kubafilinger/termostat-higrostat/eagle/lcd-i2c/lcd-i2c-pcb.png

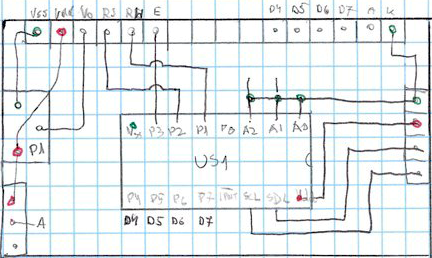
eagle/lcd-i2c/lcd-i2c-pcb.png
