kubafilinger/termostat-higrostat/eagle/relays-board/relays-board-schema.png

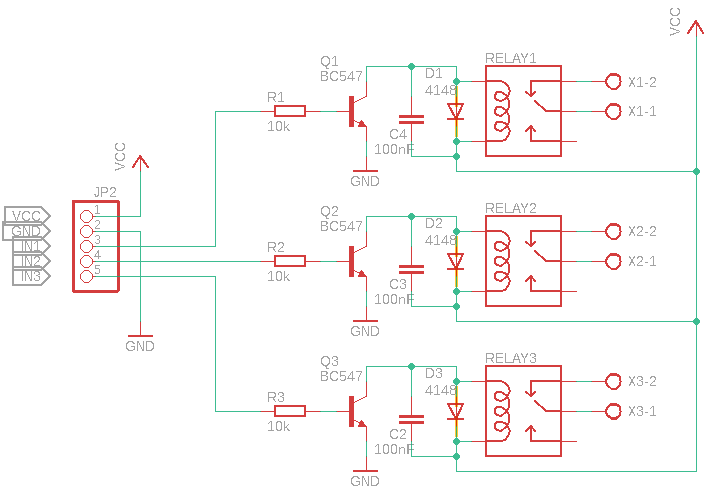
eagle/relays-board/relays-board-schema.png
