kubafilinger/termostat-higrostat/eagle/lcd-i2c/lcd-i2c.sch

## EAGLE design eagle/lcd-i2c/lcd-i2c.sch (2018-12-25)

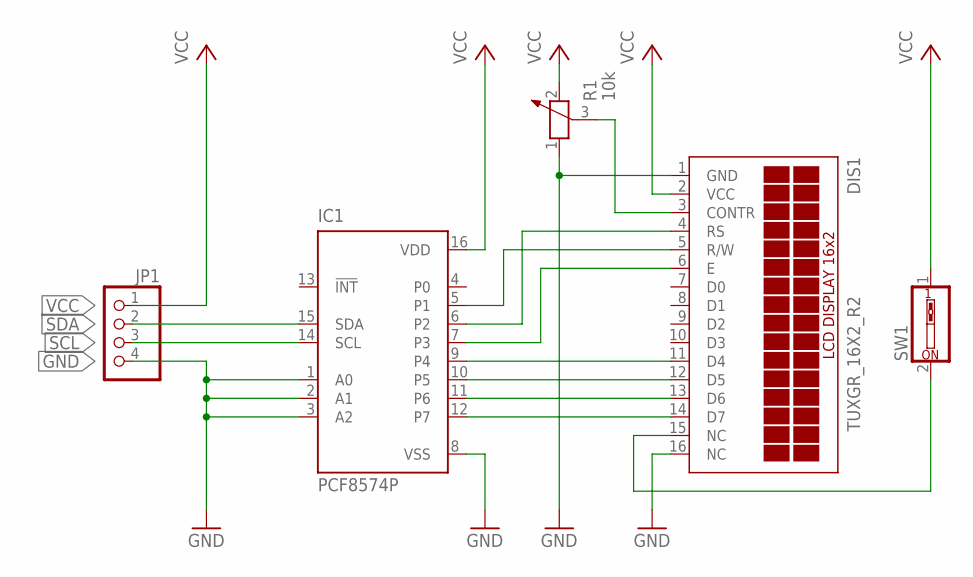
[picture p11: schematic lcd-i2c.sch]

Parts:
DIS1: TUXGR_16X2_R2
IC1: PCF8574P; DIL16
JP1: PINHD-1X4/90; 1X04/90
R1: 10k; PT-10S
SW1: SW_DIP-1; EDG-01

Connections:
GND: DIS1.1 (GND), DIS1.16 (NC), IC1.1 (A0), IC1.2 (A1), IC1.3 (A2), IC1.8 (VSS), JP1.4, R1.1
unnamed: DIS1.13 (D6), IC1.11 (P6)
unnamed: DIS1.15 (NC), SW1.2
unnamed: DIS1.14 (D7), IC1.12 (P7)
unnamed: DIS1.12 (D5), IC1.10 (P5)
unnamed: DIS1.11 (D4), IC1.9 (P4)
unnamed: DIS1.6 (E), IC1.7 (P3)
unnamed: DIS1.5 (R/W), IC1.5 (P1)
unnamed: DIS1.4 (RS), IC1.6 (P2)
unnamed: DIS1.3 (CONTR), R1.3
SCL: IC1.14 (SCL), JP1.3
SDA: IC1.15 (SDA), JP1.2
VCC: DIS1.2 (VCC), IC1.16 (VDD), JP1.1, R1.2, SW1.1
