kubafilinger/termostat-higrostat/eagle/mainboard/mainboard.sch

## EAGLE design eagle/mainboard/mainboard.sch (2019-04-16)

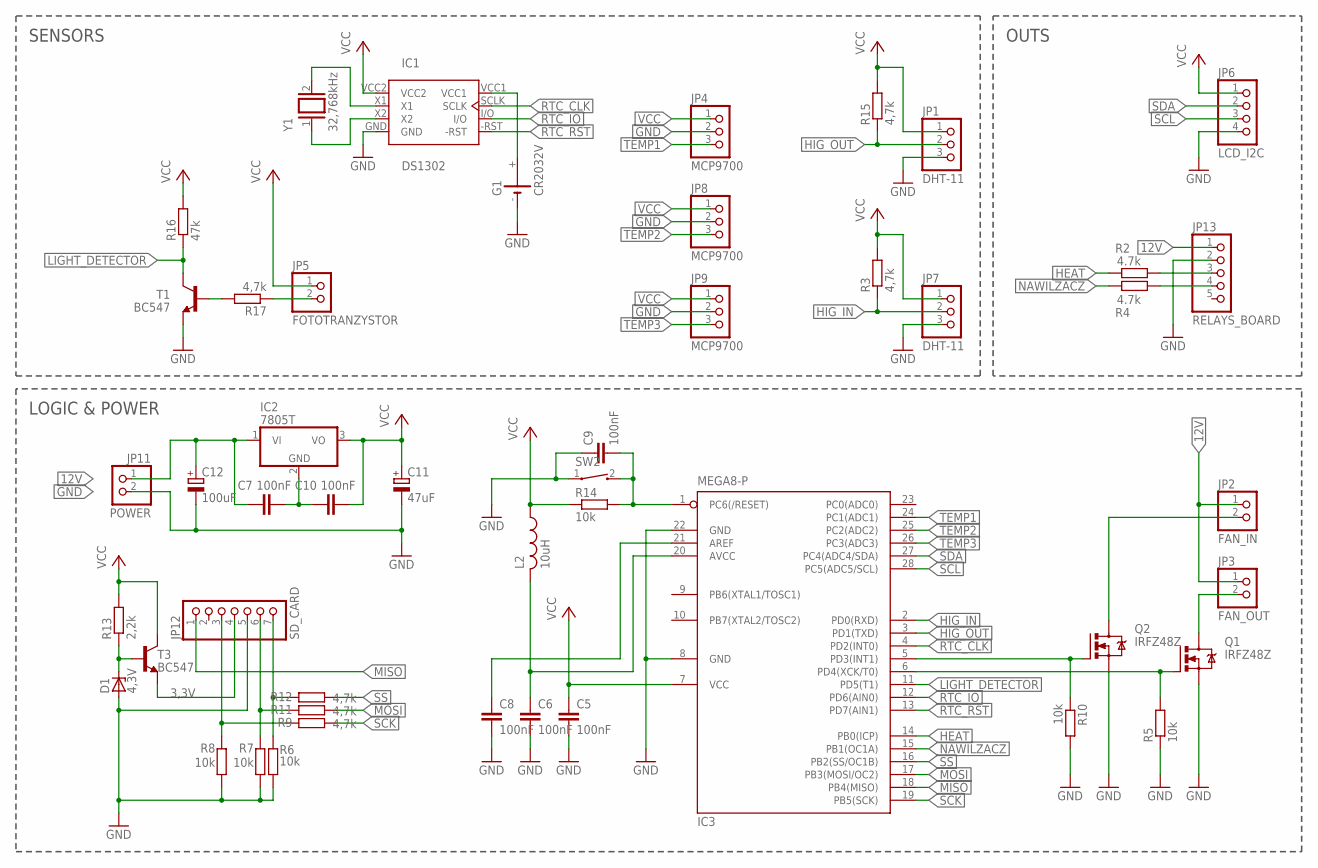
[picture p12: schematic mainboard.sch]

Parts:
C5, C6, C8, C9: 100nF; C050-030X075
C7, C10: 100nF; C050-024X044
C11: 47uF; E2,5-6
C12: 100uF; E2,5-6
D1: 4,3V; C1702-15
G1: CR2032V
IC1: DS1302; DIL08
IC2: 7805T; TO220H
IC3: MEGA8-P; DIL28-3
JP1, JP7: DHT-11; 1X03
JP2: FAN_IN; 1X02
JP3: FAN_OUT; 1X02
JP4, JP8, JP9: MCP9700; 1X03
JP5: FOTOTRANZYSTOR; 1X02
JP6: LCD_I2C; 1X04
JP11: POWER; 1X02
JP12: SD_CARD; 1X07
JP13: RELAYS_BOARD; 1X05
L2: 10uH; 0204/7
Q1, Q2: IRFZ48Z; TO220BH
R2, R4: 4.7k; 0207/10
R3, R9, R11, R12, R15, R17: 4,7k; 0207/10
R5, R6, R7, R8, R10: 10k; 0207/10
R13: 2,2k; 0207/10
R14: 10k; 0204/7
R16: 47k; 0207/10
SW2: CT10-XXXX-G4
T1, T3: BC547; TO92
Y1: 32,768kHz; QS

Connections:
3,3V: JP12.4, T3.1 (E)
12V: C7.1, C12.+, IC2.1 (VI), JP2.1, JP3.1, JP11.1, JP13.1
GND: C5.2, C6.2, C8.2, C9.1, C11.-, C12.-, D1.A, G1.-, IC1.GND, IC3.8 (GND), IC3.22 (GND), JP1.3, JP4.2, JP6.4, JP7.3, JP8.2, JP9.2, JP11.2, JP12.5, JP13.2, Q1.S, Q2.S, R5.1, R6.1, R7.1, R8.1, R10.2, SW2.1, T1.1 (E)
HEAT: IC3.14 (PB0(ICP)), R2.1
HIG_IN: IC3.2 (PD0(RXD)), JP7.2, R3.1
HIG_OUT: IC3.3 (PD1(TXD)), JP1.2, R15.1
LIGHT_DETECTOR: IC3.6 (PD4(XCK/T0)), IC3.11 (PD5(T1)), Q1.G, R5.2, R16.1, T1.3 (C)
MISO: IC3.18 (PB4(MISO)), JP12.1
MOSI: IC3.17 (PB3(MOSI/OC2)), R11.1
unnamed: JP13.3, R2.2
unnamed: IC1.X1, Y1.2
unnamed: JP13.4, R4.1
unnamed: C9.2, IC3.1 (PC6(/RESET)), R14.2, SW2.2
unnamed: JP5.2, R17.1
unnamed: C6.1, IC3.20 (AVCC), L2.2
unnamed: C8.1, IC3.21 (AREF)
unnamed: IC1.X2, Y1.1
unnamed: C7.2, C10.1, IC2.2 (GND)
unnamed: IC3.5 (PD3(INT1)), Q2.G, R10.1
unnamed: D1.C, R13.1, T3.2 (B)
unnamed: R17.2, T1.2 (B)
unnamed: JP2.2, Q2.D
unnamed: JP12.7, R6.2, R12.2
unnamed: JP3.2, Q1.D
unnamed: JP12.6, R7.2, R11.2
unnamed: JP12.3, R8.2, R9.2
NAWILZACZ: IC3.15 (PB1(OC1A)), R4.2
RTC_CLK: IC1.SCLK, IC3.4 (PD2(INT0))
RTC_IO: IC1.I/O, IC3.12 (PD6(AIN0))
RTC_RST: IC1.-RST, IC3.13 (PD7(AIN1))
SCK: IC3.19 (PB5(SCK)), R9.1
SCL: IC3.28 (PC5(ADC5/SCL)), JP6.3
SDA: IC3.27 (PC4(ADC4/SDA)), JP6.2
SS: IC3.16 (PB2(SS/OC1B)), R12.1
TEMP1: IC3.24 (PC1(ADC1)), JP4.3
TEMP2: IC3.25 (PC2(ADC2)), JP8.3
TEMP3: IC3.26 (PC3(ADC3)), JP9.3
VCC: C5.1, C10.2, C11.+, IC1.VCC2, IC2.3 (VO), IC3.7 (VCC), JP1.1, JP4.1, JP5.1, JP6.1, JP7.1, JP8.1, JP9.1, L2.1, R3.2, R13.2, R14.1, R15.2, R16.2, T3.3 (C)
VCC1: G1.+, IC1.VCC1

Notes on the sheet:
SENSORS
OUTS
LOGIC & POWER
