kubafilinger/termostat-higrostat/eagle/nawilzacz/nawilzacz.sch

## EAGLE design eagle/nawilzacz/nawilzacz.sch (2018-12-25)

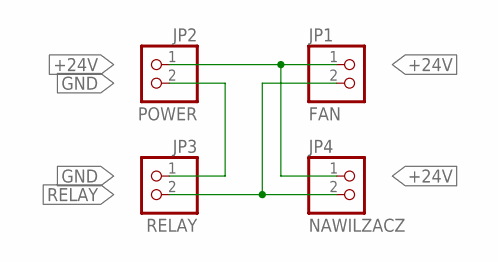
[picture p13: schematic nawilzacz.sch]

Parts:
JP1: FAN; 1X02
JP2: POWER; 1X02
JP3: RELAY; 1X02
JP4: NAWILZACZ; 1X02

Connections:
+24V: JP1.1, JP2.1, JP4.1
GND: JP2.2, JP3.1
RELAY: JP1.2, JP3.2, JP4.2
