kubafilinger/termostat-higrostat/eagle/relays-board/relays-board.sch

## EAGLE design eagle/relays-board/relays-board.sch (2018-12-25)

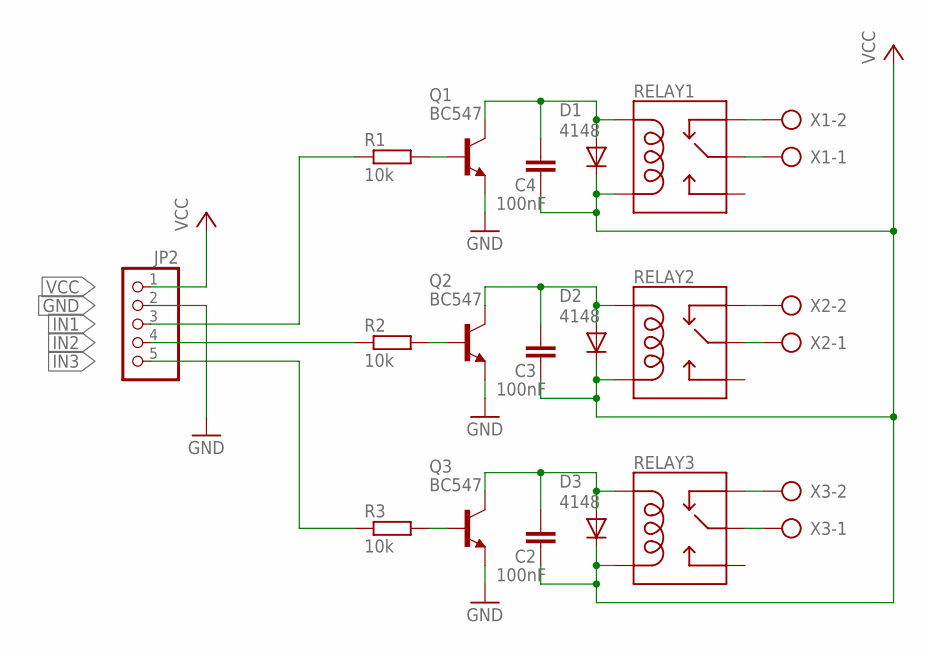
[picture p14: schematic relays-board.sch]

Parts:
C2, C3, C4: 100nF; C025-025X050
D1, D2, D3: 4148; DO35-10
JP2: PINHD-1X5; 1X05
Q1, Q2, Q3: BC547; TO92
R1, R2, R3: 10k; 0207/10
RELAY1, RELAY2, RELAY3: RELAYPTH; SRD-05VDC-SL-C
X1, X2, X3: AK300/2

Connections:
GND: JP2.2, Q1.1 (E), Q2.1 (E), Q3.1 (E)
IN1: JP2.3, R1.1
IN2: JP2.4, R2.1
IN3: JP2.5, R3.1
unnamed: RELAY3.SWCOMMON, X3.1
unnamed: RELAY3.SWCLOSED (SWCLOSE), X3.2
unnamed: Q1.2 (B), R1.2
unnamed: RELAY2.SWCLOSED (SWCLOSE), X2.2
unnamed: RELAY2.SWCOMMON, X2.1
unnamed: RELAY1.SWCOMMON, X1.1
unnamed: RELAY1.SWCLOSED (SWCLOSE), X1.2
unnamed: C2.1, D3.A, Q3.3 (C), RELAY3.COIL1
unnamed: C3.1, D2.A, Q2.3 (C), RELAY2.COIL1
unnamed: C4.1, D1.A, Q1.3 (C), RELAY1.COIL1
unnamed: Q2.2 (B), R2.2
unnamed: Q3.2 (B), R3.2
VCC: C2.2, C3.2, C4.2, D1.C, D2.C, D3.C, JP2.1, RELAY1.COIL0, RELAY2.COIL0, RELAY3.COIL0
